miki4148/nixie_driver_dren/files/NixieDriverTwoTubes/img/NixieDriverTwoTubes_ANGLE.png

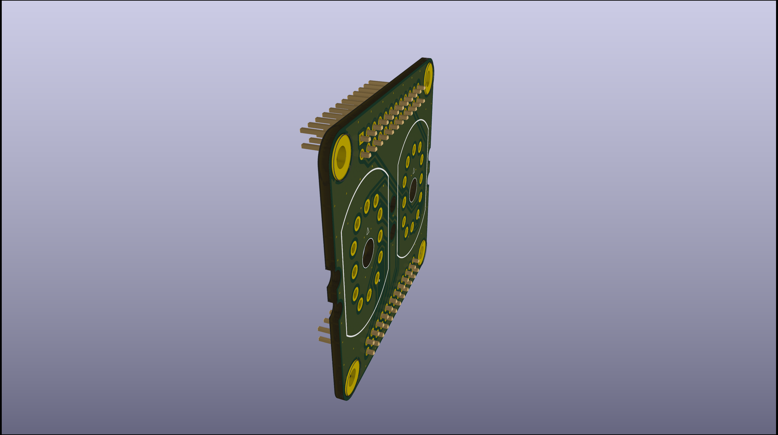
files/NixieDriverTwoTubes/img/NixieDriverTwoTubes_ANGLE.png
